JeremyBois/Ptechinos/data/doc/Pogo_4pins_2.5P_RightAngle.png

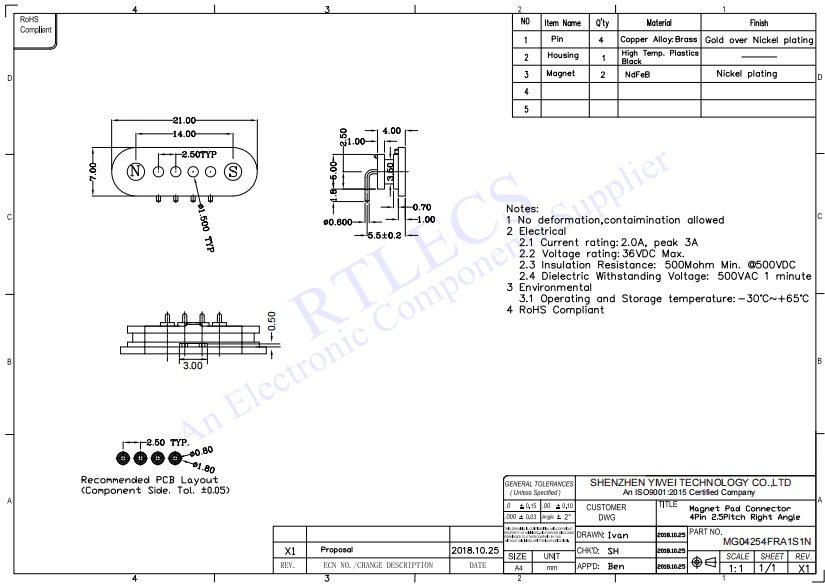
data/doc/Pogo_4pins_2.5P_RightAngle.png
