JeremyBois/Ptechinos/data/doc/Pogo_4pins_2.5P_Straight.png

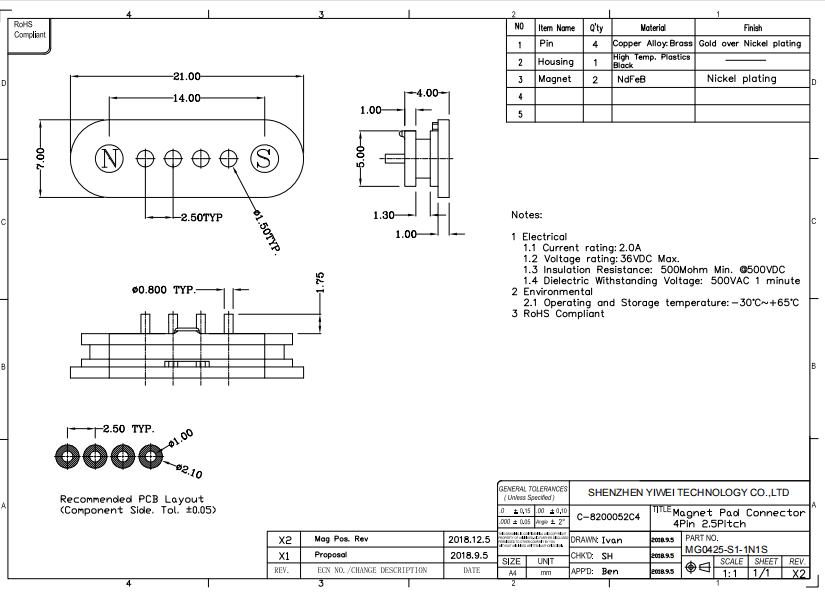
data/doc/Pogo_4pins_2.5P_Straight.png
