JeremyBois/Ptechinos/data/sources/design/friends_flying.png

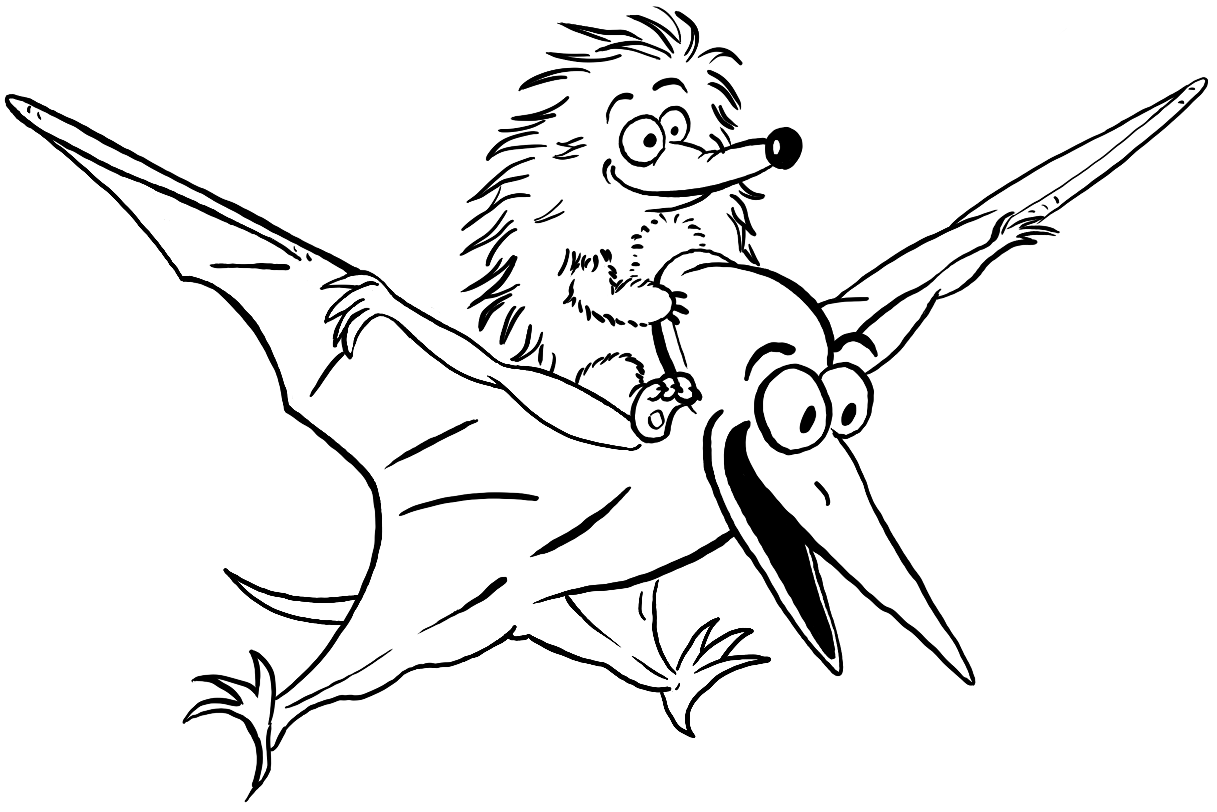
data/sources/design/friends_flying.png
