JeremyBois/Ptechinos/data/sources/design/hedgehog.png

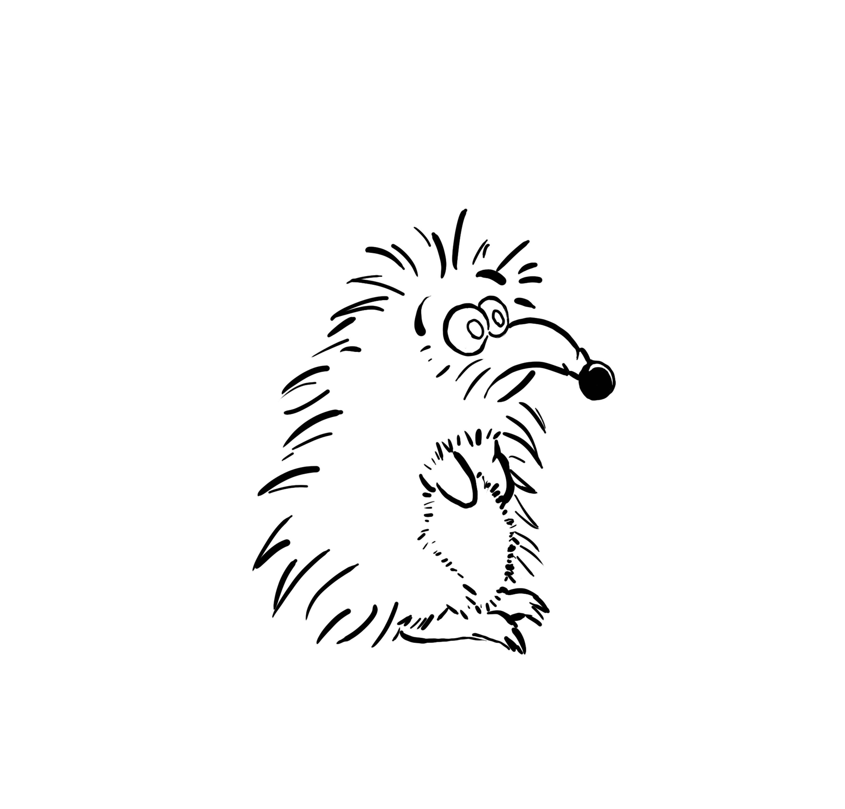
data/sources/design/hedgehog.png
