JeremyBois/Ptechinos/data/sources/design/hedgehog_shadow_flipped.png

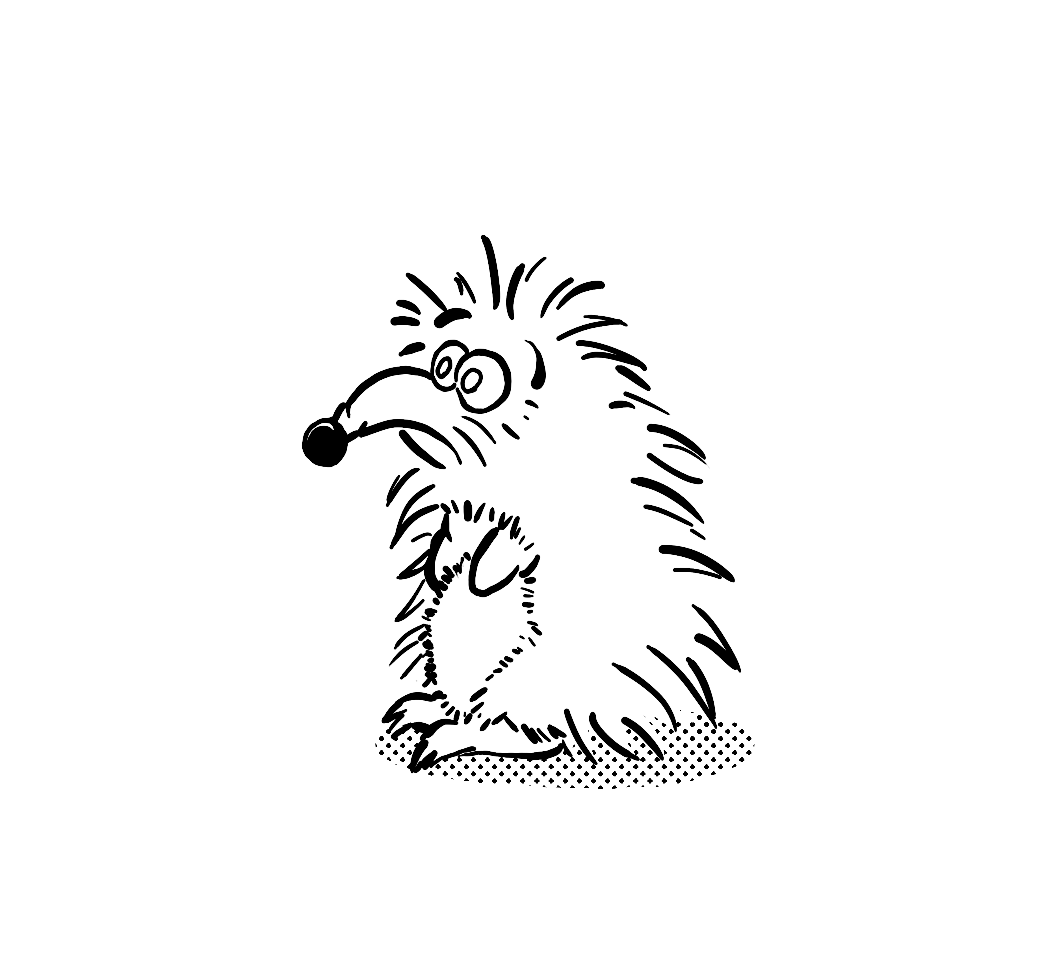
data/sources/design/hedgehog_shadow_flipped.png
