JeremyBois/Ptechinos/data/sources/design/pterodactyl.png

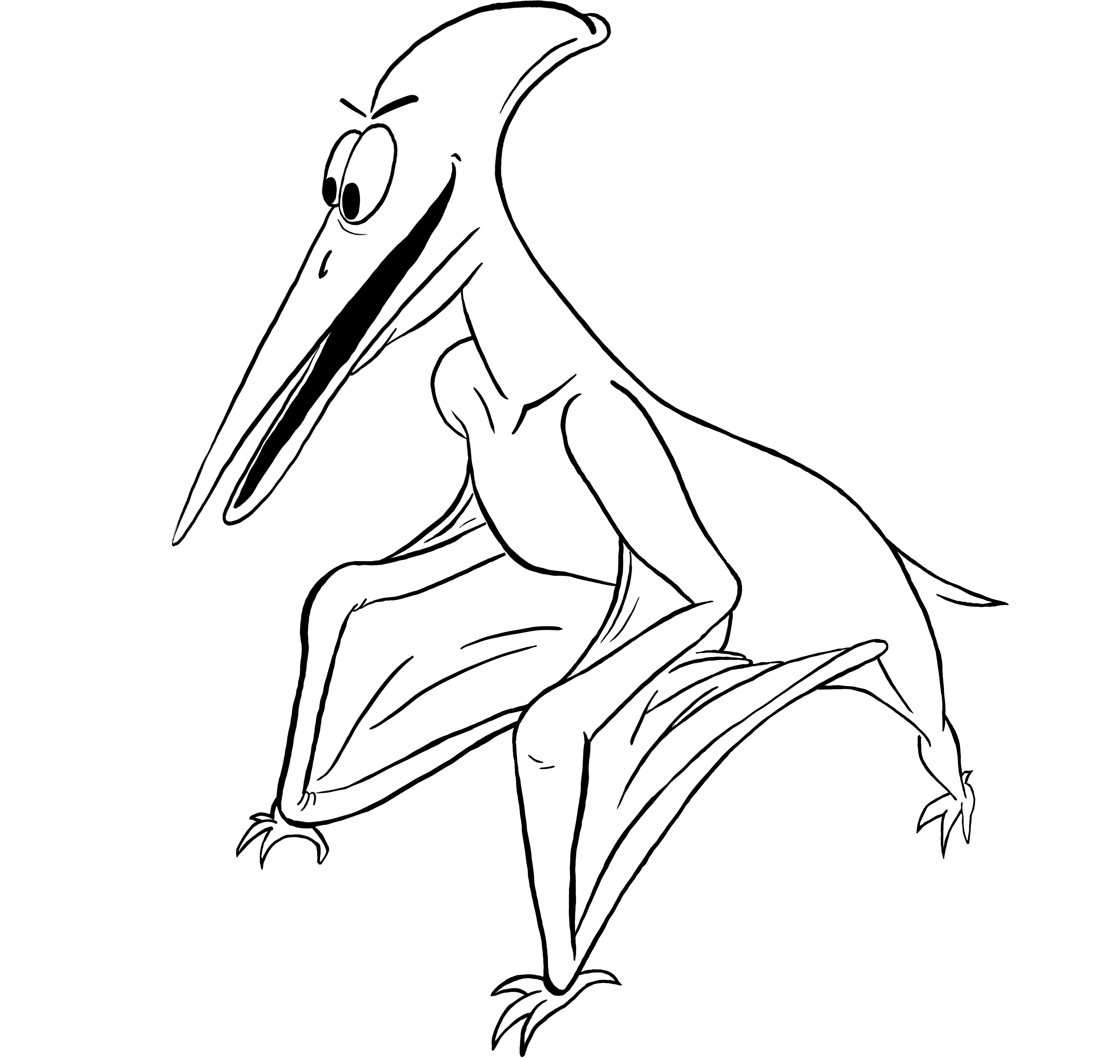
data/sources/design/pterodactyl.png
