JeremyBois/Ptechinos/data/sources/design/pterodactyl_shadow.png

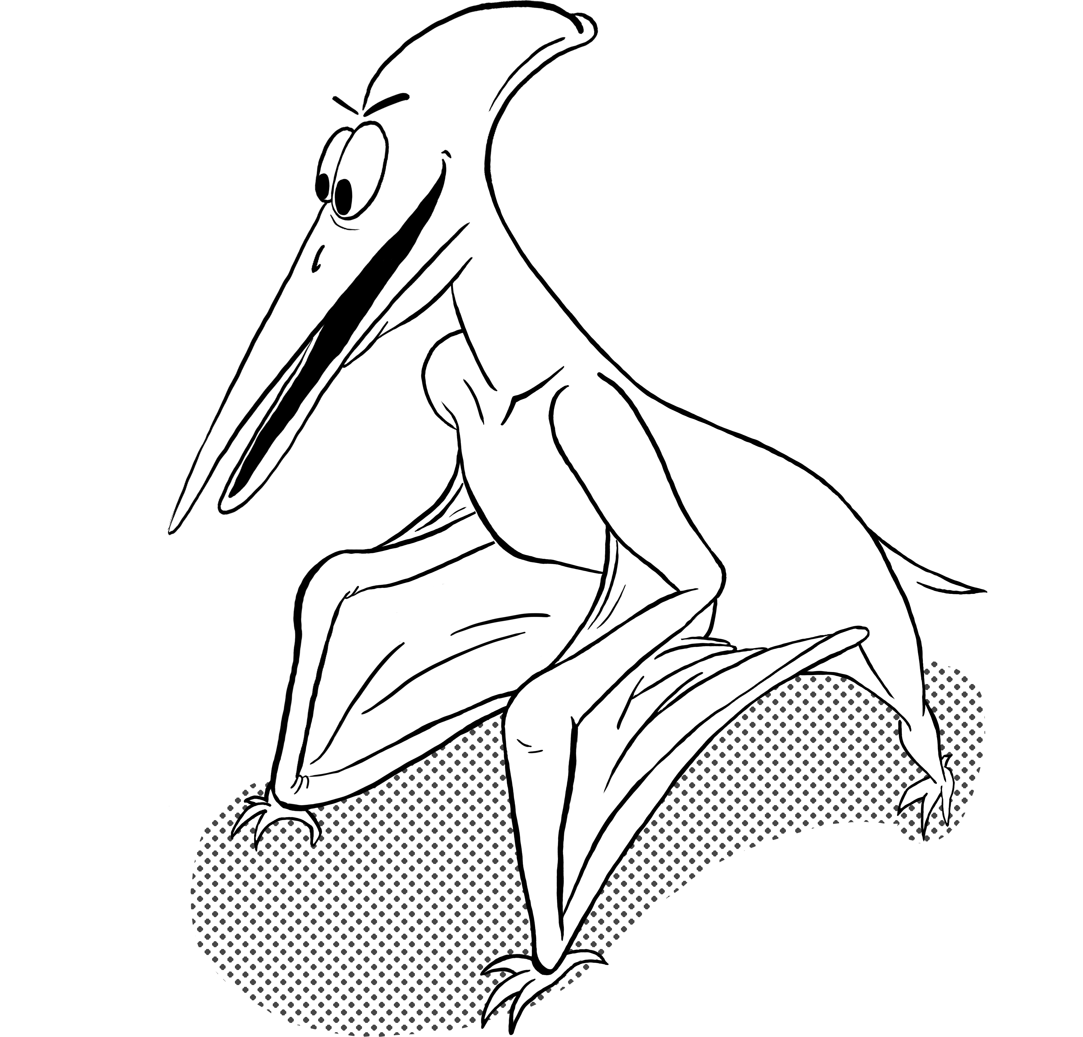
data/sources/design/pterodactyl_shadow.png
