JeremyBois/Ptechinos/data/sources/design/pterodactyl_shadow_flipped.png

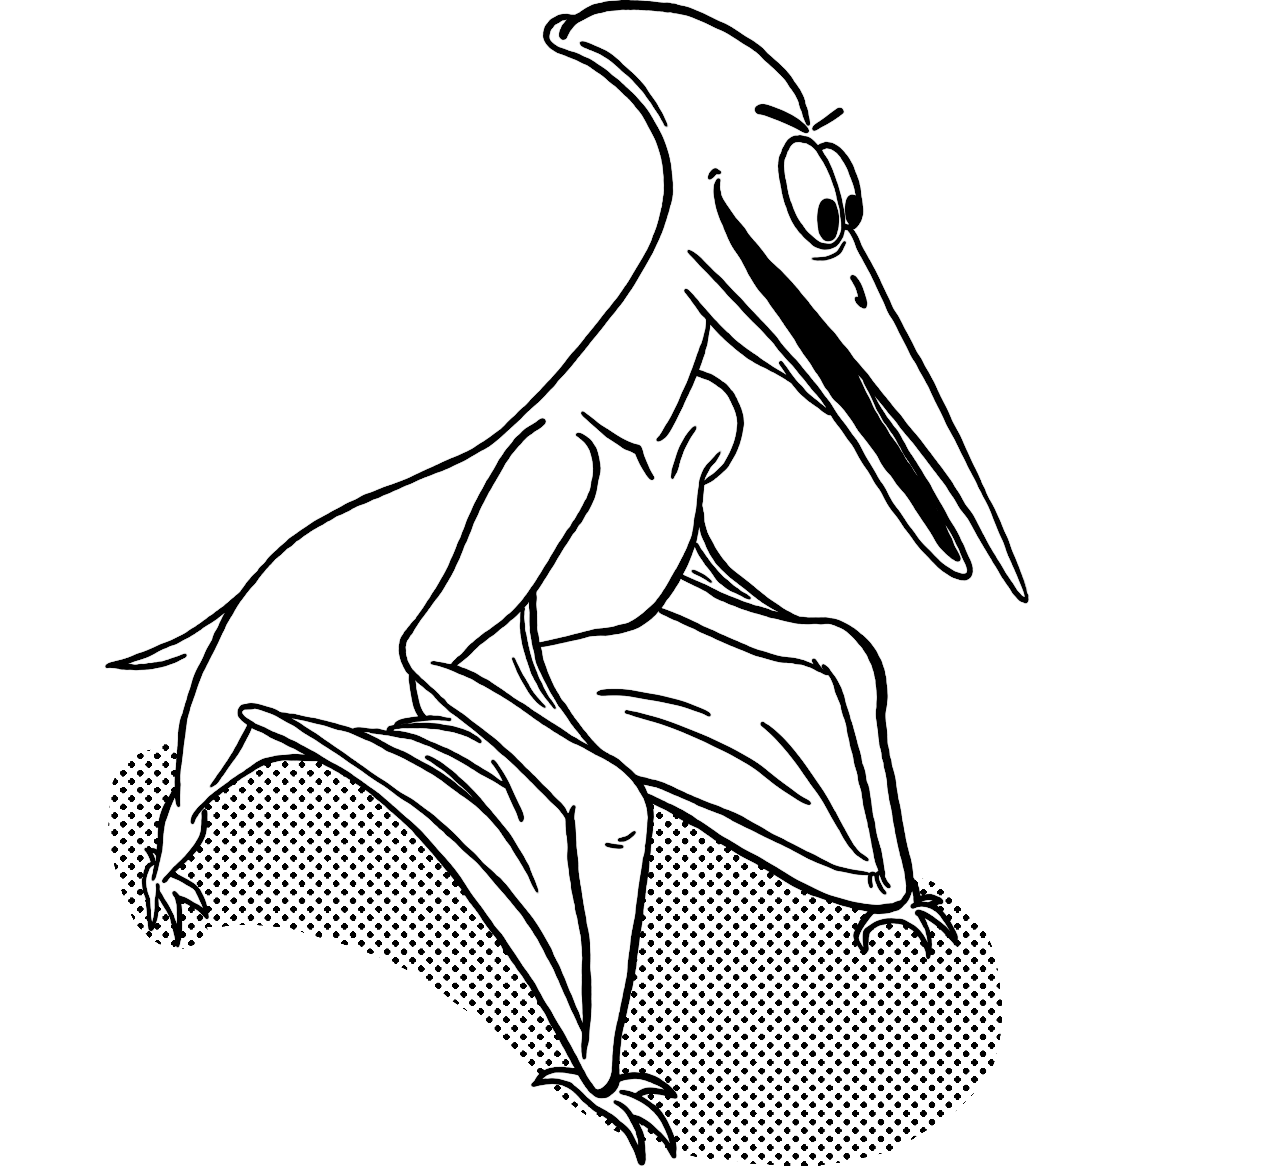
data/sources/design/pterodactyl_shadow_flipped.png
