JeremyBois/Ptechinos/data/models/JST_SH_8pins_Vertical.step

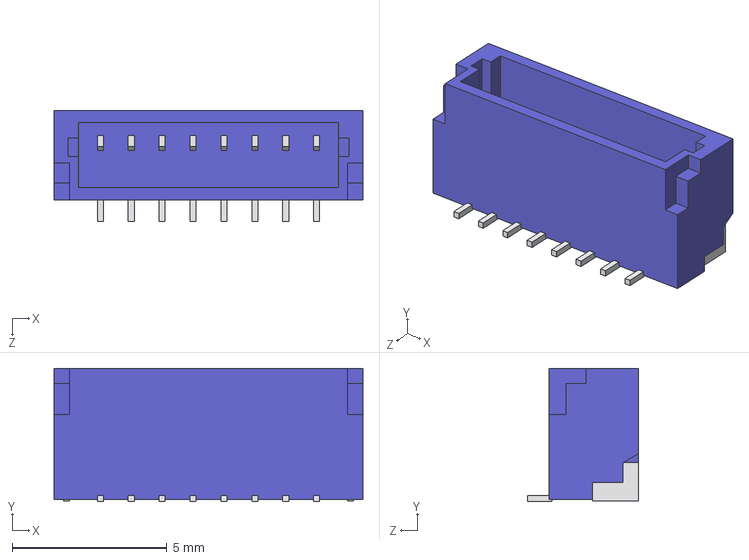
[picture p23: CAD file, 2022-11-18]
data/models/JST_SH_8pins_Vertical.step
10.0 x 4.32 x 3.60 mm
