JeremyBois/Ptechinos/data/models/TRRS_3.5mm.step

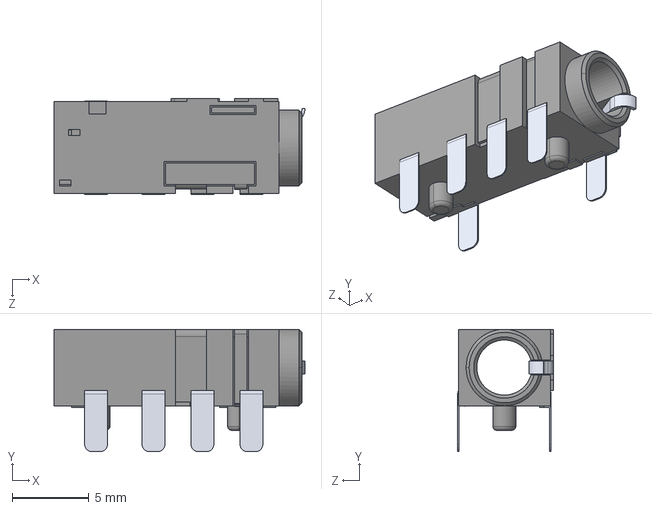
[picture p24: CAD file, 2022-11-18]
data/models/TRRS_3.5mm.step
16.4 x 8.00 x 6.25 mm
