JeremyBois/Ptechinos/data/models/Pogo_4pins_RightAngle.step

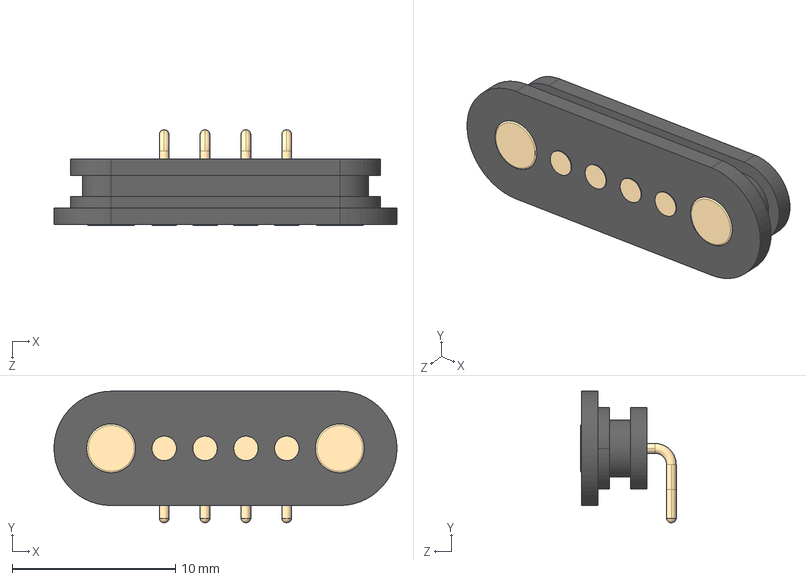
[picture p25: CAD file, 2022-11-18]
data/models/Pogo_4pins_RightAngle.step
21.0 x 8.06 x 5.85 mm
plastique
contacts
pinout x 4
