JeremyBois/Ptechinos/data/production/v0.3/keycaps.dxf

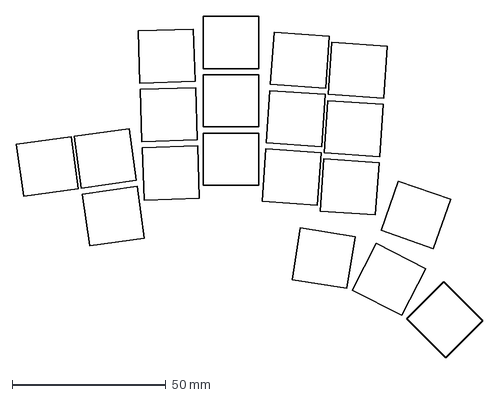
[picture p26: CAD file, 2022-04-24, an earlier design]
data/production/v0.3/keycaps.dxf
151.5 x 111.0 mm
