JeremyBois/Ptechinos/ptechinos.kicad_sch

## KiCad design ptechinos.kicad_sch (2022-11-20)

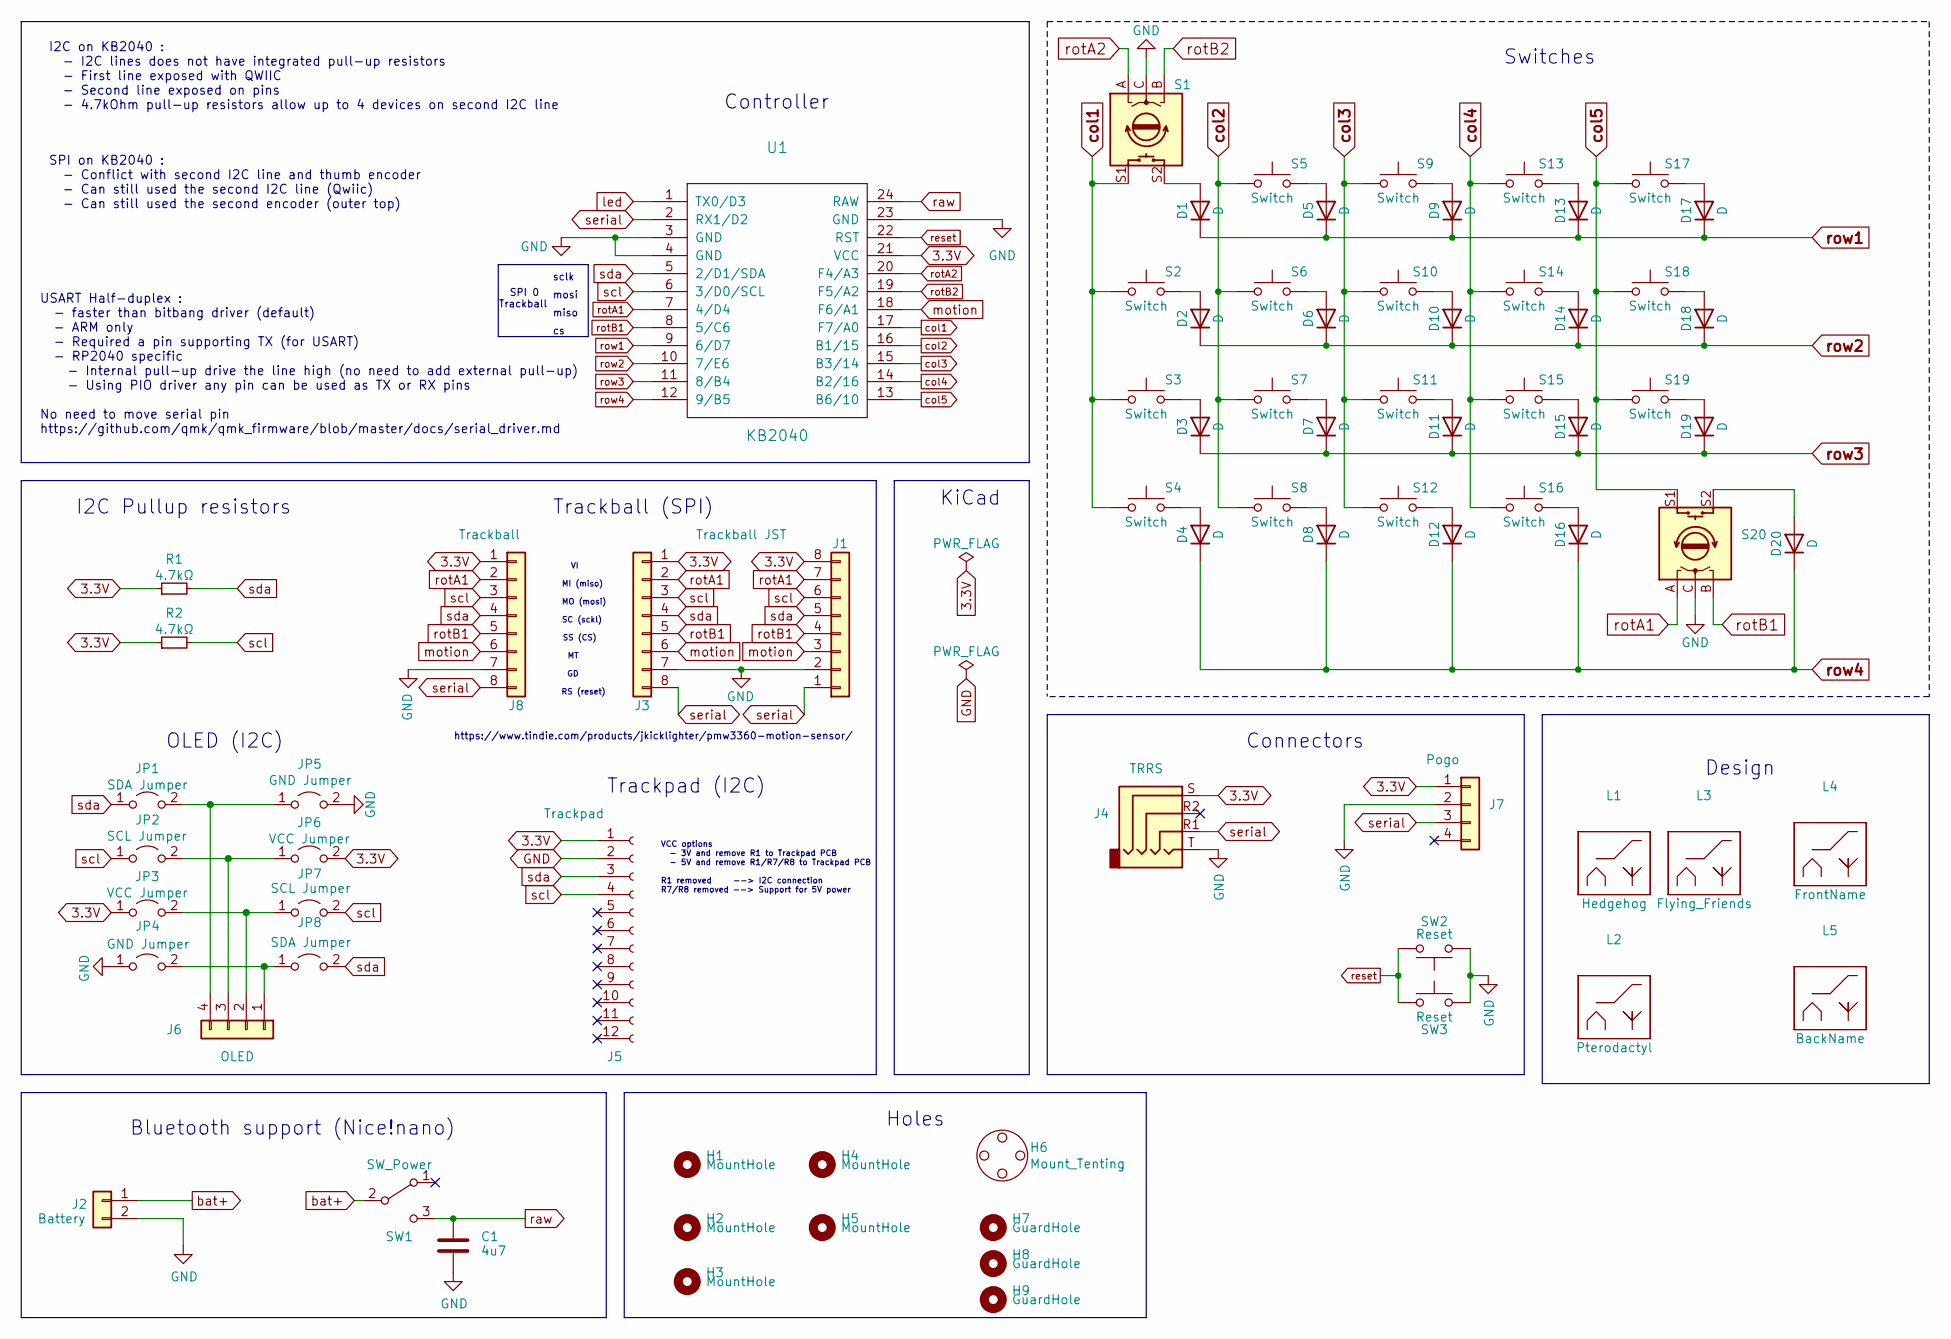
[picture p35: schematic ptechinos.kicad_sch]

Parts:
C1: 4u7; C_0805_2012Metric
D1, D2, D3, D4, D5, D6, D7, D8, D9, D10, D11, D12, D13, D14, D15, D16, D17, D18, D19, D20: D; D3_TH_SMD_v2
H1, H2, H3, H4, H5: MountHole; M2_Mount_Hole
H6: Mount_Tenting; Tenting_Puck
H7, H8, H9: GuardHole; M2_Guard_Hole
J1: Trackball (Serial); JST_SH_BM08B-SRSS-TB_1x08-1MP_P1.00mm_Vertical
J2: Battery; JST_PH_S2B-PH-K_1x02_P2.00mm_Horizontal
J3: Trackball JST; JST_SH_BM08B-SRSS-TB_1x08-1MP_P1.00mm_Vertical
J4: TRRS; MJ-4PP-9
J5: Trackpad; GCT_FFC2B35-12-G_R
J6: OLED
J7: Pogo; Pogo_1x04_P2.5mm
J8: Trackball; PMW3360
JP1, JP8: SDA Jumper; Jumper_open
JP2, JP7: SCL Jumper; Jumper_open
JP3, JP6: VCC Jumper; Jumper_open
JP4, JP5: GND Jumper; Jumper_open
L1: Hedgehog; hedgehog-shadow-medium
L2: Pterodactyl; pterodactyl-shadow-medium
L3: Flying_Friends; flying-friends-medium
L4: FrontName; board_name
L5: BackName; board_name
R1, R2: 4.7kΩ; R_0805_2012Metric
S1, S20: RotaryEncoder_Switch; pg1350-EVQWGD001_R
S2, S3, S4, S5, S6, S7, S8, S9, S10, S11, S12, S13, S14, S15, S16, S17, S18, S19: Switch; Kailh_socket_PG1350_optional_reversible.kicad_mod
SW1: SW_Power; SW_MSK12C02_ShouHan_reversible
SW2, SW3: Reset; SW_SKRKAEE020_ALPS
U1: KB2040

Connections:
3.3V: J1.8, J3.1, J4.S, J5.1, J7.1, J8.1, JP3.1 (A), JP6.2 (B), R1.1, R2.1, U1.21 (VCC)
GND: C1.2, J1.2, J2.2, J3.7, J4.T, J5.2, J7.2, J8.7, JP4.1 (A), JP5.2 (B), S1.C, S20.C, SW2.1, SW3.2, U1.3 (GND), U1.4 (GND), U1.23 (GND)
unnamed: D1.2 (A), S1.S2
unnamed: D2.2 (A), S2.2
unnamed: D3.2 (A), S3.2
unnamed: D4.2 (A), S4.2
unnamed: D5.2 (A), S5.2
unnamed: D6.2 (A), S6.2
unnamed: D7.2 (A), S7.2
unnamed: D8.2 (A), S8.2
unnamed: D9.2 (A), S9.2
unnamed: D10.2 (A), S10.2
unnamed: D11.2 (A), S11.2
unnamed: D12.2 (A), S12.2
unnamed: D13.2 (A), S13.2
unnamed: D14.2 (A), S14.2
unnamed: D15.2 (A), S15.2
unnamed: D16.2 (A), S16.2
unnamed: D17.2 (A), S17.2
unnamed: D18.2 (A), S18.2
unnamed: D19.2 (A), S19.2
unnamed: D20.2 (A), S20.S2
unnamed: J6.1, JP4.2 (B), JP8.1 (A)
unnamed: J6.2, JP3.2 (B), JP7.1 (A)
unnamed: J6.3, JP2.2 (B), JP6.1 (A)
unnamed: J6.4, JP1.2 (B), JP5.1 (A)
bat+: J2.1, SW1.2 (B)
col1: S1.S1, S2.1, S3.1, S4.1, U1.17 (F7/A0)
col2: S5.1, S6.1, S7.1, S8.1, U1.16 (B1/15)
col3: S9.1, S10.1, S11.1, S12.1, U1.15 (B3/14)
col4: S13.1, S14.1, S15.1, S16.1, U1.14 (B2/16)
col5: S17.1, S18.1, S19.1, S20.S1, U1.13 (B6/10)
led: U1.1 (TX0/D3)
motion: J1.3, J3.6, J8.6, U1.18 (F6/A1)
raw: C1.1, SW1.3 (C), U1.24 (RAW)
reset: SW2.2, SW3.1, U1.22 (RST)
rotA1: J1.7, J3.2, J8.2, S20.A, U1.7 (4/D4)
rotA2: S1.A, U1.20 (F4/A3)
rotB1: J1.4, J3.5, J8.5, S20.B, U1.8 (5/C6)
rotB2: S1.B, U1.19 (F5/A2)
row1: D1.1 (K), D5.1 (K), D9.1 (K), D13.1 (K), D17.1 (K), U1.9 (6/D7)
row2: D2.1 (K), D6.1 (K), D10.1 (K), D14.1 (K), D18.1 (K), U1.10 (7/E6)
row3: D3.1 (K), D7.1 (K), D11.1 (K), D15.1 (K), D19.1 (K), U1.11 (8/B4)
row4: D4.1 (K), D8.1 (K), D12.1 (K), D16.1 (K), D20.1 (K), U1.12 (9/B5)
scl: J1.6, J3.3, J5.4, J8.3, JP2.1 (A), JP7.2 (B), R2.2, U1.6 (3/D0/SCL)
sda: J1.5, J3.4, J5.3, J8.4, JP1.1 (A), JP8.2 (B), R1.2, U1.5 (2/D1/SDA)
serial: J1.1, J3.8, J4.R1, J7.3, J8.8, U1.2 (RX1/D2)

Notes on the sheet:
RS (reset)
Holes
I2C on KB2040 : - I2C lines does not have integrated pull-up resistors - First line exposed with QWIIC - Second line exposed on pins - 4.7kOhm pull-up resistors allow up to 4 devices on second I2C line
MI (miso)
MO (mosi)
Connectors
KiCad
I2C Pullup resistors
miso
Trackpad (I2C)
SC (sckl)
Trackball (SPI)
SPI on KB2040 : - Conflict with second I2C line and thumb encoder - Can still used the second I2C line (Qwiic) - Can still used the second encoder (outer top)
https://www.tindie.com/products/jkicklighter/pmw3360-motion-sensor/
USART Half-duplex : - faster than bitbang driver (default) - ARM only - Required a pin supporting TX (for USART) - RP2040 specific - Internal pull-up drive the line high (no need to add external pull-up) - Using PIO driver any pin can be used as TX or RX pins No need to move serial pin https://gith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
SPI 0 Trackball
Switches
SS (CS)
VCC options - 3V and remove R1 to Trackpad PCB - 5V and remove R1/R7/R8 to Trackpad PCB R1 removed --> I2C connection R7/R8 removed --> Support for 5V power
Bluetooth support (Nice!nano)
Design
OLED (I2C)
sclk
mosi
Controller
